kicajsky/colorofon_V2/Colorofon2026.asc

C1: cap; 10µ
C2: cap; 22n
C3: cap; 22n
C4: cap; 4.7µ; V=35 Irms=8.4m Rser=1.5 Lser=550f
C5: cap; 100p
C6: cap; 6.8n
C7: cap; 6.8n
C11: cap; 6.8n
C12: cap; 6.8n
C14: cap; 4.7µ; V=35 Irms=8.4m Rser=1.5 Lser=550f
C15: cap; 100p
C16: cap; 4.7n
C17: cap; 2.2µ; V=35 Irms=8.4m Rser=1.5 Lser=550f mfg="Würth Elektronik" pn="865250540001 WCAP-ASNP 4.3x4.3" type="Al electrolytic"
C18: cap; 10µ
C20: cap; 10µ
D1: diode; 1N4148
D2: LED
D5: diode; 1N4148
D6: LED
D7: diode; 1N4148
D8: LED
Q1: npn; BC547B
Q2: pnp
Q5: npn; BC547B
Q6: pnp
Q7: npn; BC547B
Q8: pnp
R1: res; 100k
R2: res; 10K
R3: res; 100k
R4: res; 510k
R5: res; 5.1k
R6: res; 5.6k
R7: res; 10K
R8: res; 100
R9: res; 93k
R10: res; 560
R11: res; 5.6k
R12: res; 330k
R13: res; 10k
R14: res; 5.6k
R15: res; 330k
R16: res; 560
R17: res; 5.6k
R18: res; 5k
R19: res; 5.1k
R20: res; 5k
R31: res; 100
R32: res; 560
R33: res; 560
R34: res; 5.1k
R35: res; 10k
R36: res; 10K
R37: res; 330k
R39: res; 5.6k
R41: res; 100
R42: res; 560
R43: res; 560
R44: res; 10k
U1: UniversalOpAmp
U2: UniversalOpAmp
U3: UniversalOpAmp
U5: UniversalOpAmp
U6: UniversalOpAmp
U7: UniversalOpAmp
V1: voltage; SINE(0 500m 20 0 0 0 200); AC 0.5; Rser=1
V8: voltage; 12
Named nets: 0, +6V, +12V
.tran 1
.ac oct 100 1 20k
1-4k +27dB
5-18kHz 34dB
20-300Hz +28dB
potencjometr
potencjometr
